grezeh/larva/larva2 graphics/larva_pcb_silkart v2.bmp

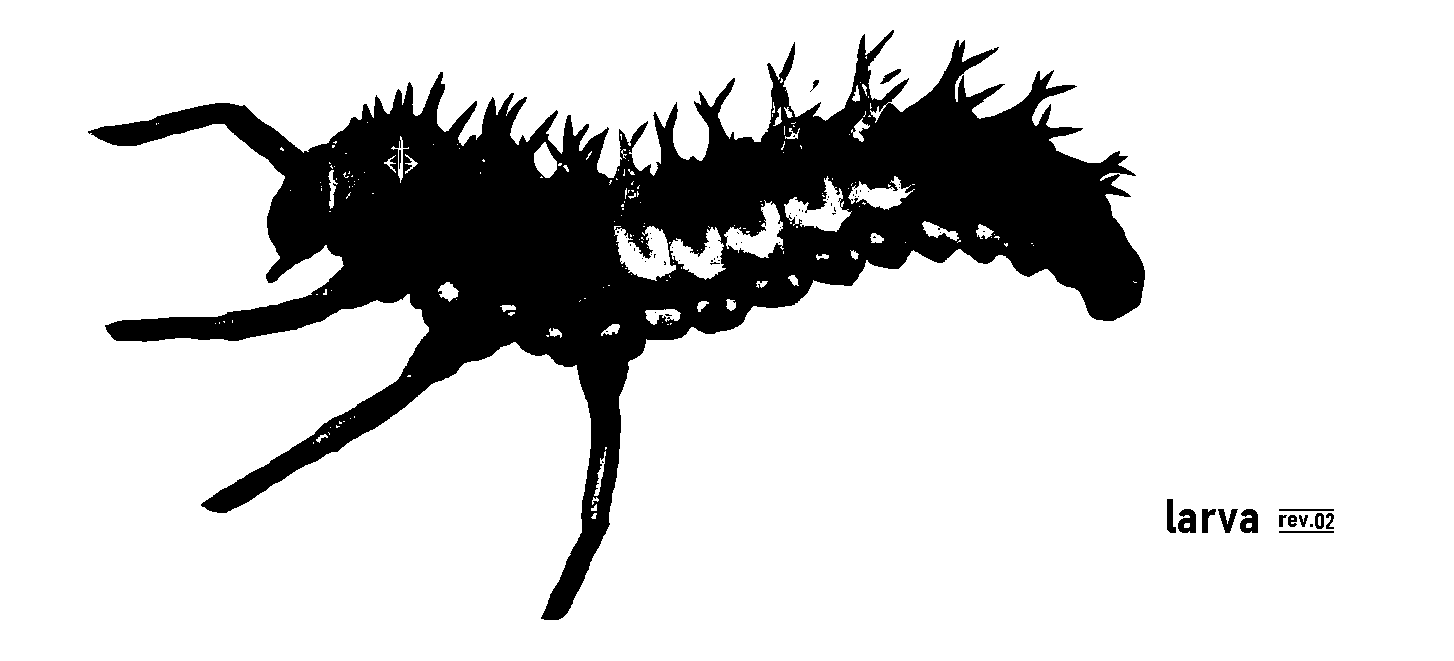
larva2 graphics/larva_pcb_silkart v2.bmp
